BensonRSI/Saba_Module/src/demo.h

const uint8_t demo_data[] = {
   0x55,0x00,0x70,0xb1,0xb4,0xb5,0xb0,0x64,
   0x68,0x5c,0x20,0x21,0x53,0x28,0x00,0xd0,
   0x2a,0x08,0xb2,0x28,0x09,0x23,0x2a,0x08,
   0xb8,0x28,0x08,0xd8,0x2a,0x0f,0x67,0x20,
   0x28,0x53,0x20,0x40,0x51,0x28,0x08,0x78,
   0x33,0x84,0x0e,0x20,0xc0,0x51,0x28,0x08,
   0x78,0x16,0x55,0x28,0x00,0x8f,0x90,0xeb,
   0x2a,0x0f,0x67,0x20,0x01,0x50,0x20,0x01,
   0x53,0x20,0x00,0x51,0x28,0x08,0x78,0x43,
   0xc0,0x53,0x25,0x28,0x84,0x0e,0x20,0xc0,
   0x51,0x28,0x08,0x78,0x16,0x55,0x28,0x00,
   0x8f,0x90,0xe7,0x90,0xc0,0x20,0xc0,0x51,
   0x28,0x08,0x8d,0x20,0x00,0x51,0x28,0x08,
   0x8d,0x20,0x40,0x51,0x28,0x08,0x8d,0x20,
   0x80,0x51,0x28,0x08,0x8d,0x29,0x08,0x5d,
   0x08,0x28,0x01,0x07,0x20,0x7a,0x52,0x28,
   0x09,0x6d,0x32,0x41,0x13,0x51,0x28,0x09,
   0x6d,0x28,0x01,0x1e,0x0c,0x08,0x28,0x01,
   0x07,0x41,0x50,0x20,0x3a,0x53,0x20,0x7a,
   0x52,0x28,0x09,0x6d,0x32,0x41,0x13,0x51,
   0x28,0x09,0x6d,0x40,0x51,0x33,0x82,0xef,
   0x28,0x01,0x1e,0x0c,0x28,0x08,0xc8,0x29,
   0x00,0x00,0x00,0x00,0x66,0x3a,0x09,0xa0,
   0xff,0x00,0x79,0x00,0x02,0x3a,0x09,0x82,
   0xff,0x00,0x79,0x00,0x02,0x3a,0x09,0x91,
   0x70,0xb0,0xb1,0xa1,0x18,0x94,0x09,0x70,
   0xb4,0xa4,0x18,0x94,0x03,0x90,0xf2,0x1c,
   0x60,0x69,0x16,0x5d,0x8f,0xfd,0x16,0x06,
   0x16,0x07,0x0f,0x29,0x08,0xe6,0x74,0xc3,
   0x53,0x74,0xc4,0x54,0x71,0x59,0x44,0x18,
   0xb5,0x36,0x92,0x2f,0x45,0x57,0x43,0x18,
   0xb4,0x39,0x94,0x05,0x78,0x59,0x16,0x58,
   0x48,0xc8,0x58,0x42,0x82,0x02,0x41,0x1f,
   0x82,0x0c,0xb1,0x20,0x60,0xb0,0x20,0xc0,
   0xb0,0x24,0x60,0x94,0xfd,0x37,0x84,0x06,
   0xa4,0x24,0xff,0x90,0xdc,0xa5,0x24,0xff,
   0x90,0xcf,0x1c,0x60,0x69,0x16,0x5d,0x16,
   0x5d,0x16,0x5d,0x16,0x5c,0x16,0x06,0x16,
   0x07,0x0f,0x74,0xc1,0x51,0x74,0xc2,0x52,
   0x70,0x18,0x50,0x71,0x57,0x42,0x18,0xb5,
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
};
