BensonRSI/Saba_Module/tools/sabamon/memory_window.h

#ifndef memory_window_033433
#define memory_window_033433

#include "editscreen.h"

void create_memory_window(EditScreen *screen); /* the size is from the editscreen */

#define MEMORY_WINDOW_XSIZE 21
#define MEMORY_WINDOW_YSIZE 5

#endif
