BensonRSI/Saba_Module/tools/sabamon/protocol.h

#ifndef __protocol_h_31456
#define __protocol_h_31456

#include "c_types.h"

extern void get_mem(tWord adr, tByte length, tByte *ptr);
extern void set_mem(tWord adr, tByte length, tByte *ptr);
extern void jump(tWord adr);


#endif
